tporyzala/tensile-tester/cad/Fixtures/Tensile Gripper Assy 7x7mm.SLDASM

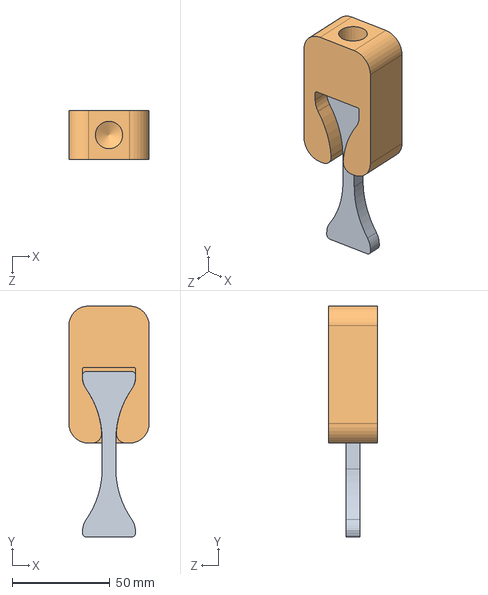
[picture p3: CAD file, 2026-06-16]
cad/Fixtures/Tensile Gripper Assy 7x7mm.SLDASM
41.0 x 117.9 x 25.0 mm
Tensile Gripper 7x7mm
Tensile Coupon 7x7mm
