tporyzala/tensile-tester/cad/Structure/Control Box Face.SLDPRT

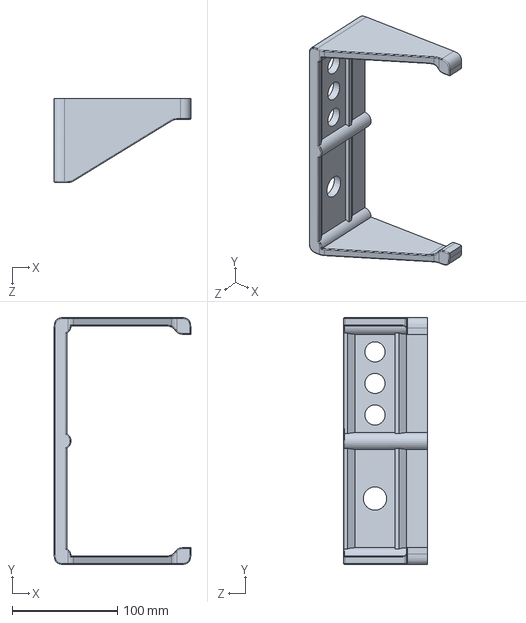
[picture p18: CAD file, 2026-06-02]
cad/Structure/Control Box Face.SLDPRT
130.0 x 235.0 x 80.0 mm
