tporyzala/tensile-tester/cad/toPrint/Tensile Gripper 7x7mm.STEP

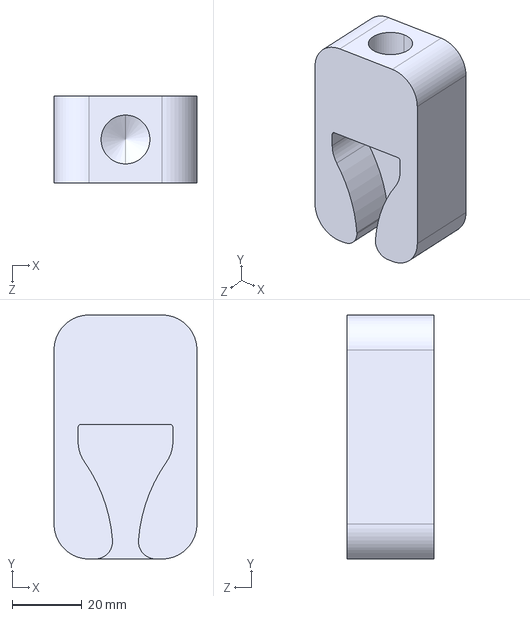
[picture p19: CAD file, 2026-06-16]
cad/toPrint/Tensile Gripper 7x7mm.STEP
41.0 x 70.0 x 25.0 mm
