tporyzala/tensile-tester/cad/Electronics/GX-16 Connector 6 Pins.SLDPRT

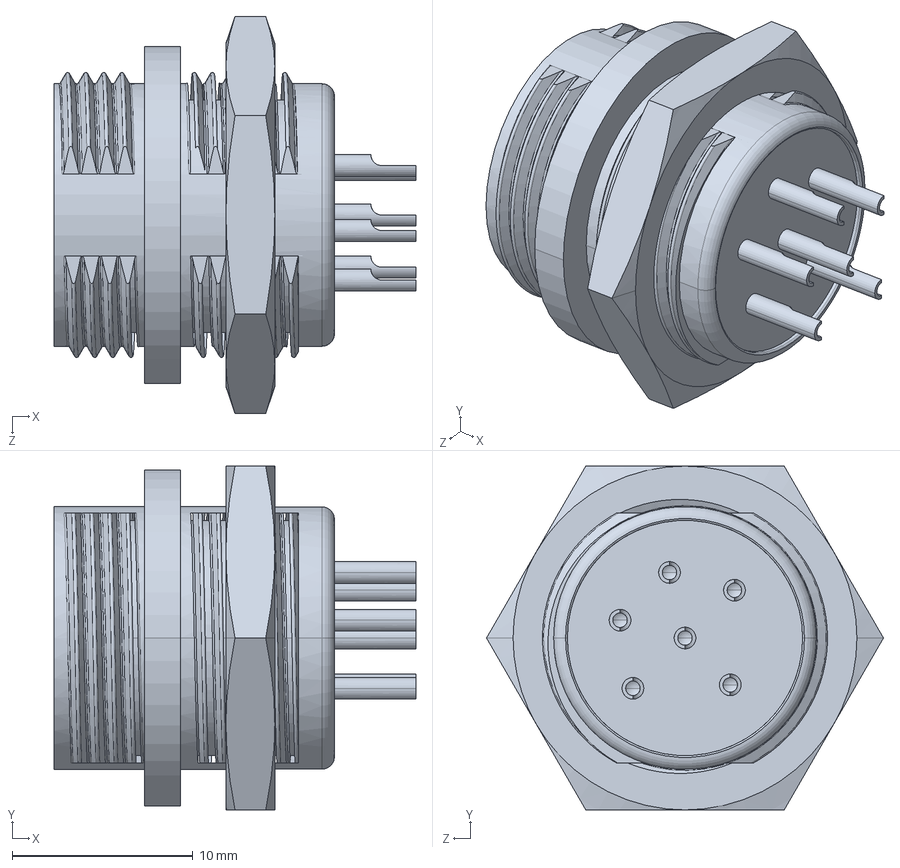
[picture p20: CAD file, 2026-01-30]
cad/Electronics/GX-16 Connector 6 Pins.SLDPRT
20.0 x 19.0 x 21.9 mm
