tporyzala/tensile-tester/cad/MGN9/MGN9 Rail.SLDPRT

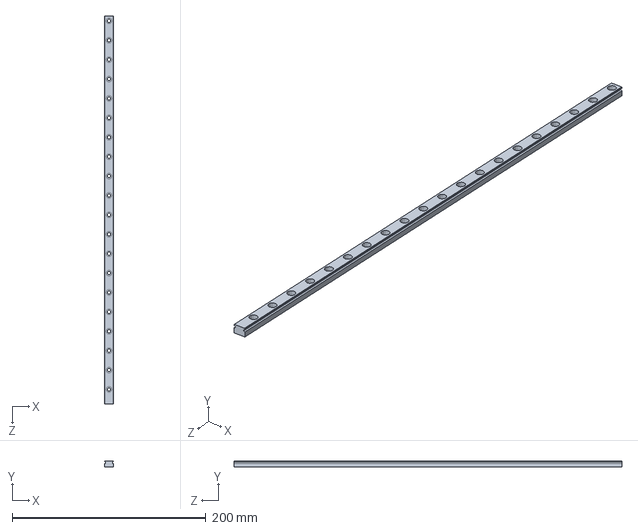
[picture p21: CAD file, 2025-11-23]
cad/MGN9/MGN9 Rail.SLDPRT
9.00 x 6.50 x 400.0 mm
