tporyzala/tensile-tester/cad/SFU/FK10.SLDPRT

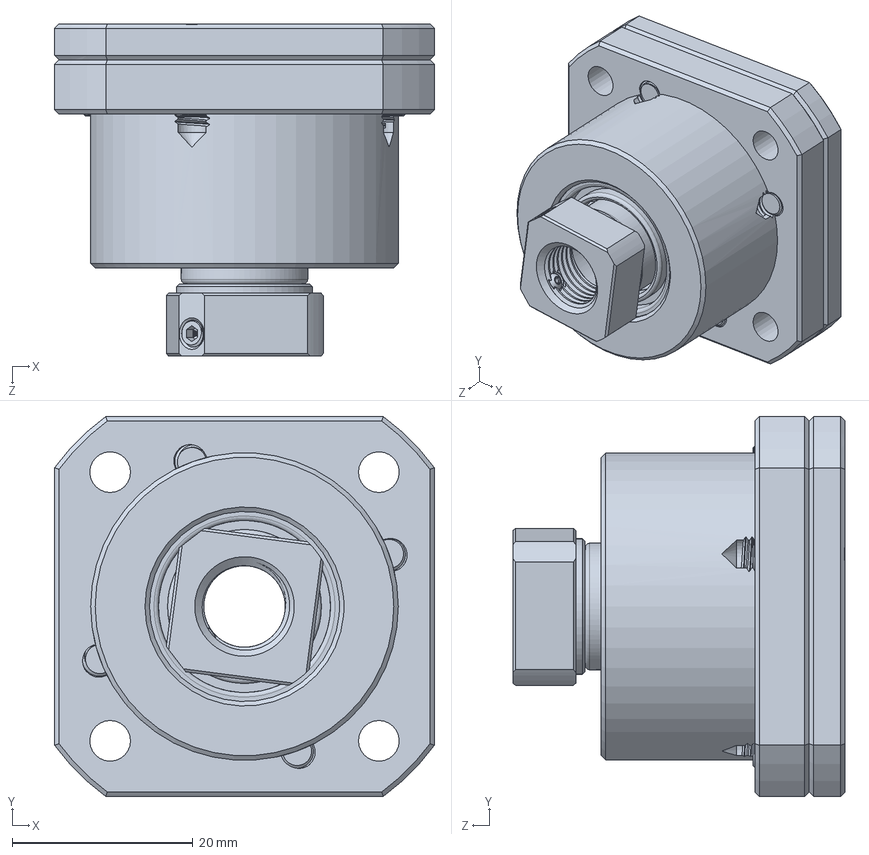
[picture p22: CAD file, 2025-11-23]
cad/SFU/FK10.SLDPRT
42.0 x 42.0 x 36.7 mm
