tporyzala/tensile-tester/cad/Structure/Control Box Base.SLDPRT

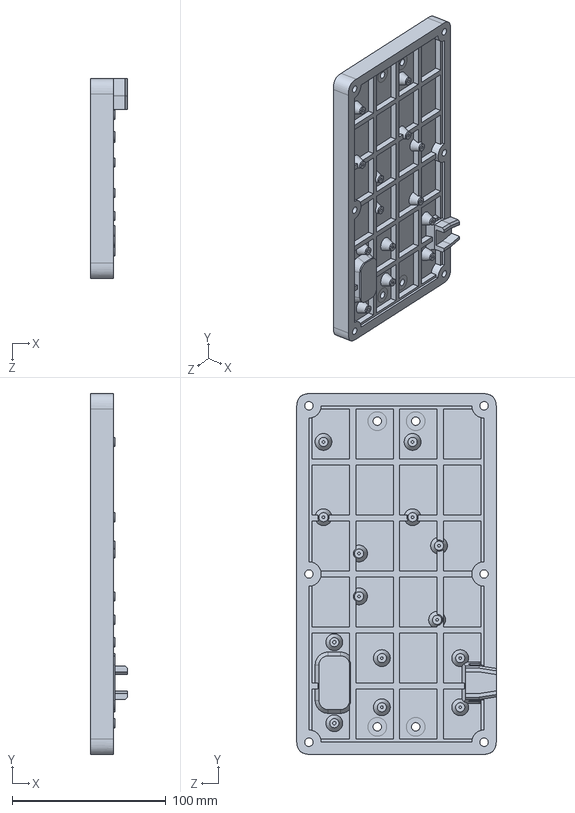
[picture p23: CAD file, 2026-06-02]
cad/Structure/Control Box Base.SLDPRT
24.0 x 235.0 x 130.0 mm
