tporyzala/tensile-tester/cad/toPrint/Tensile Coupon 7x7mm.STEP

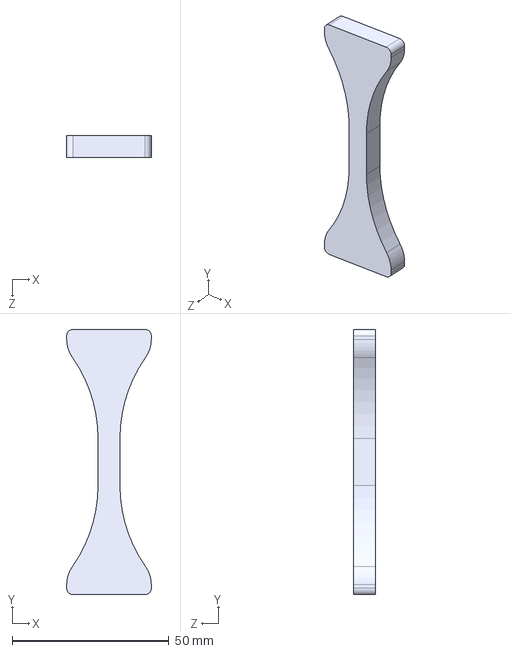
[picture p24: CAD file, 2026-06-16]
cad/toPrint/Tensile Coupon 7x7mm.STEP
27.0 x 84.5 x 7.00 mm
