tporyzala/tensile-tester/cad/Electronics/dc-dc converter.SLDPRT

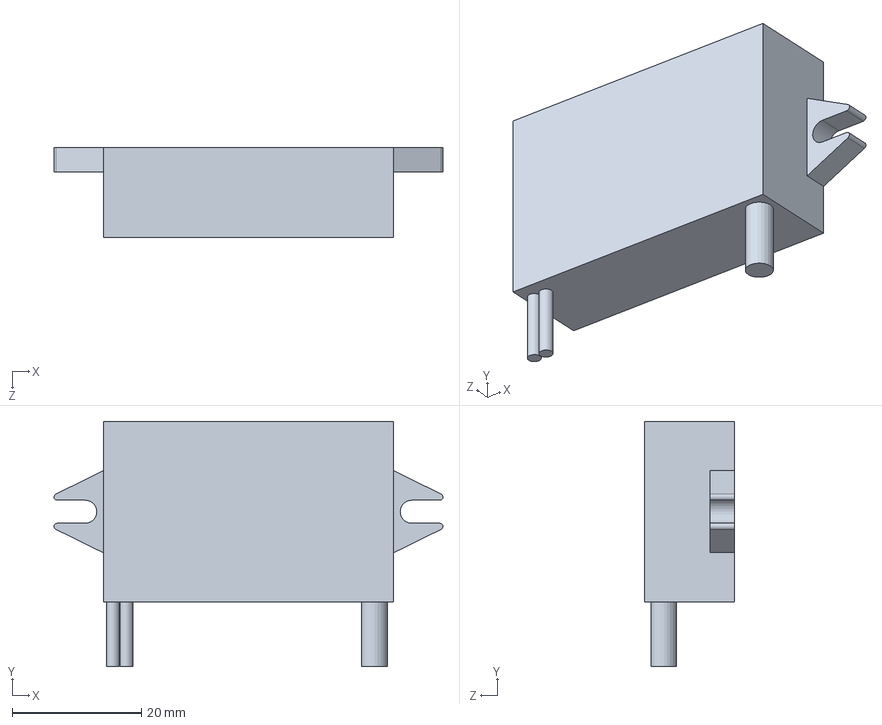
[picture p25: CAD file, 2026-01-26]
cad/Electronics/dc-dc converter.SLDPRT
60.3 x 38.0 x 14.0 mm
