tporyzala/tensile-tester/cad/SFU/BF10.SLDPRT

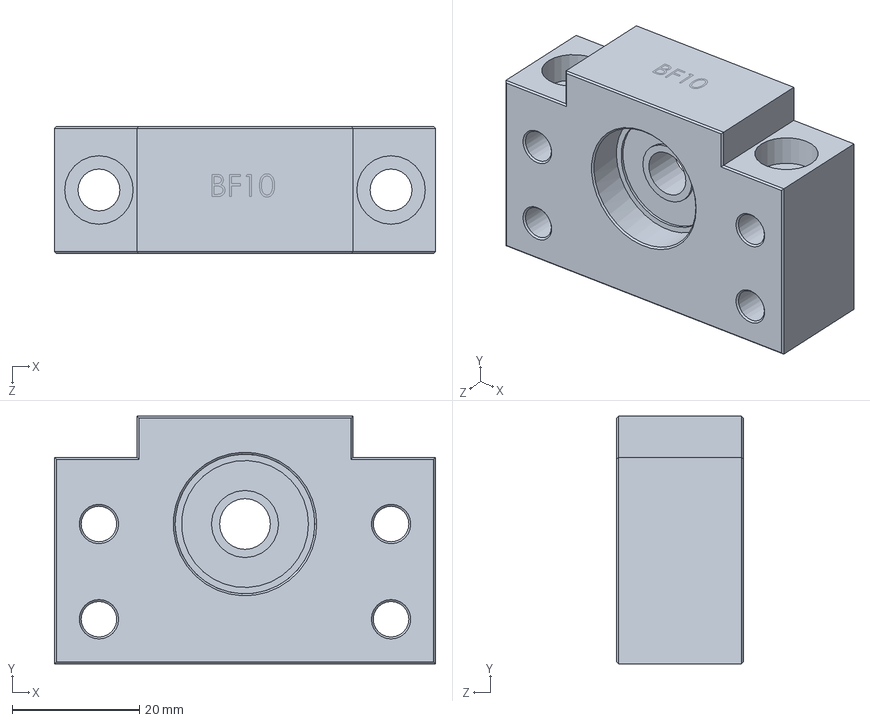
[picture p26: CAD file, 2025-11-23]
cad/SFU/BF10.SLDPRT
60.0 x 39.0 x 20.0 mm
