tporyzala/tensile-tester/cad/Structure/Amplifier Mount Block.SLDPRT

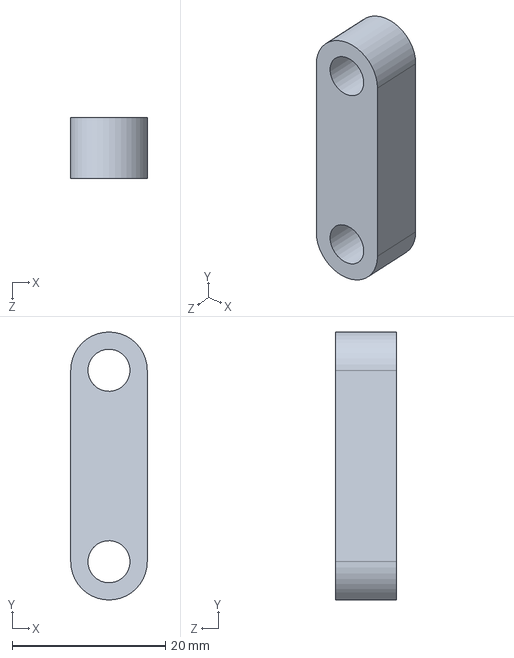
[picture p27: CAD file, 2026-05-17]
cad/Structure/Amplifier Mount Block.SLDPRT
10.0 x 35.0 x 8.00 mm
