tporyzala/tensile-tester/cad/Electronics/power distribution board.SLDPRT

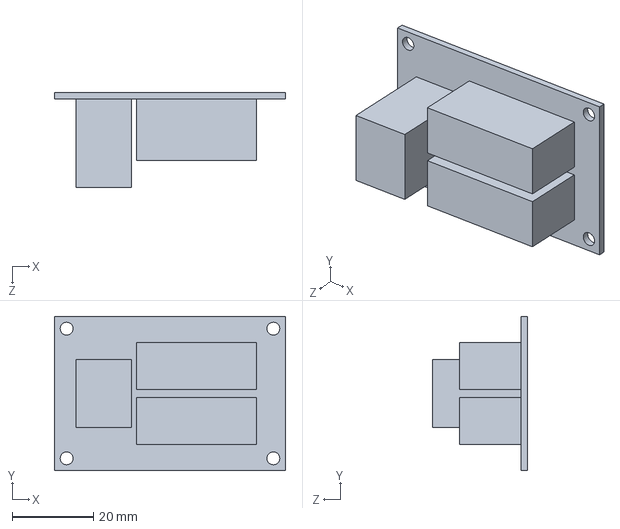
[picture p28: CAD file, 2026-01-26]
cad/Electronics/power distribution board.SLDPRT
57.0 x 38.0 x 23.4 mm
