tporyzala/tensile-tester/cad/SFU/SFU1204 Block.SLDPRT

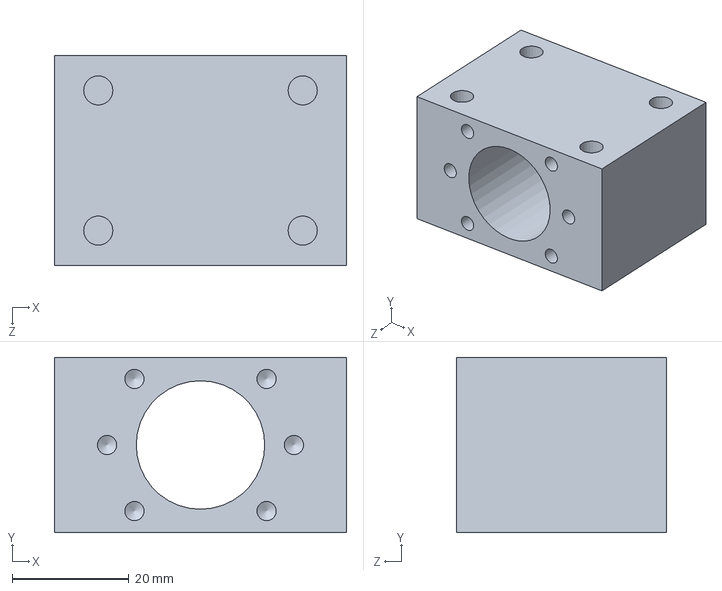
[picture p29: CAD file, 2025-11-23]
cad/SFU/SFU1204 Block.SLDPRT
50.0 x 30.0 x 36.0 mm
