tporyzala/tensile-tester/cad/toPrint/Amplifier Mount.STEP

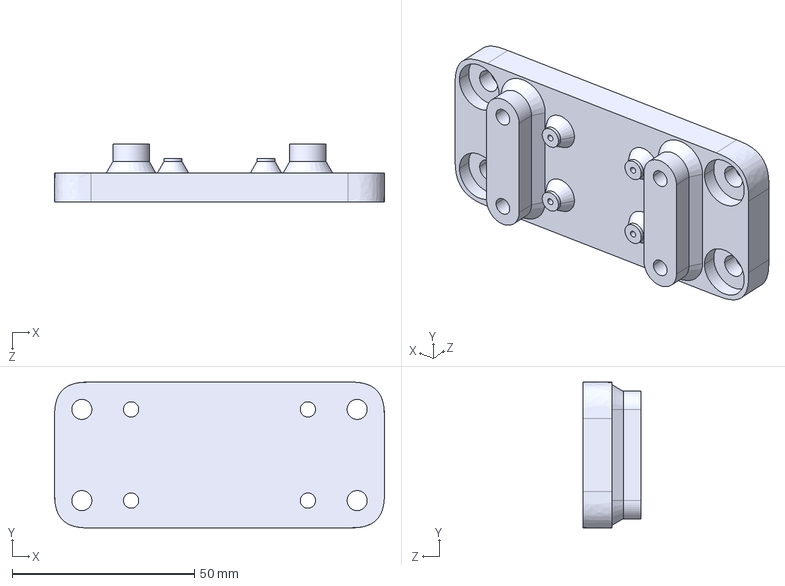
[picture p30: CAD file, 2026-05-17]
cad/toPrint/Amplifier Mount.STEP
90.5 x 40.0 x 16.0 mm
