tporyzala/tensile-tester/cad/Electronics/Raspberry Pi 4 Model B.SLDPRT

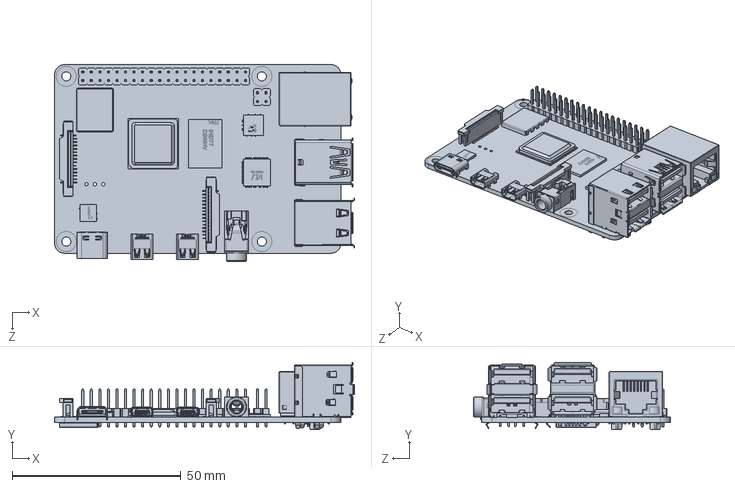
[picture p31: CAD file, 2026-01-25]
cad/Electronics/Raspberry Pi 4 Model B.SLDPRT
89.0 x 19.9 x 58.4 mm
