tporyzala/tensile-tester/cad/Structure/Top Face Plate.SLDPRT

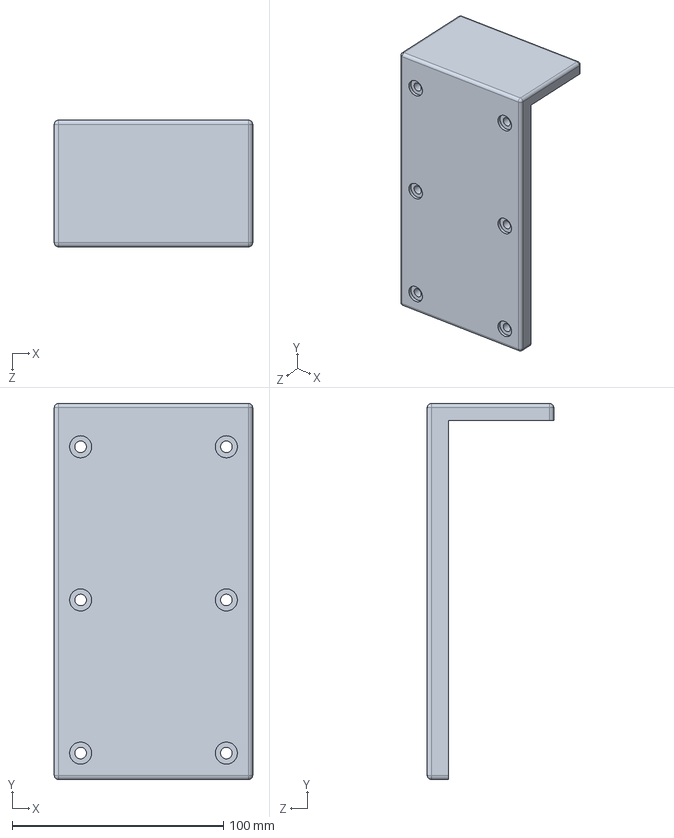
[picture p32: CAD file, 2026-01-17]
cad/Structure/Top Face Plate.SLDPRT
94.0 x 178.0 x 60.0 mm
