tporyzala/tensile-tester/cad/Electronics/HX711.SLDPRT

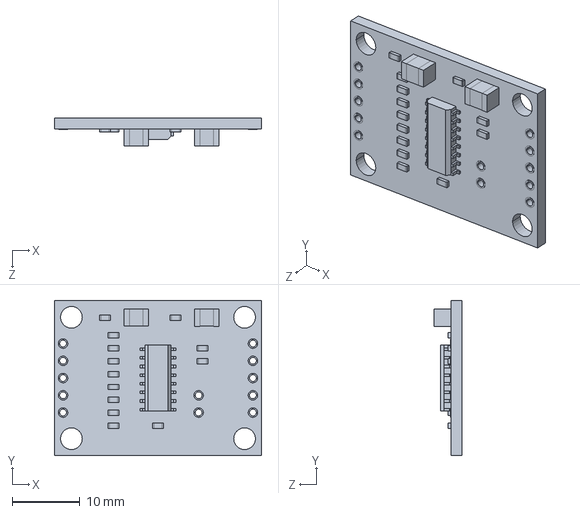
[picture p33: CAD file, 2026-01-25]
cad/Electronics/HX711.SLDPRT
30.5 x 22.9 x 4.10 mm
