tporyzala/tensile-tester/cad/Structure/Top plate column.SLDPRT

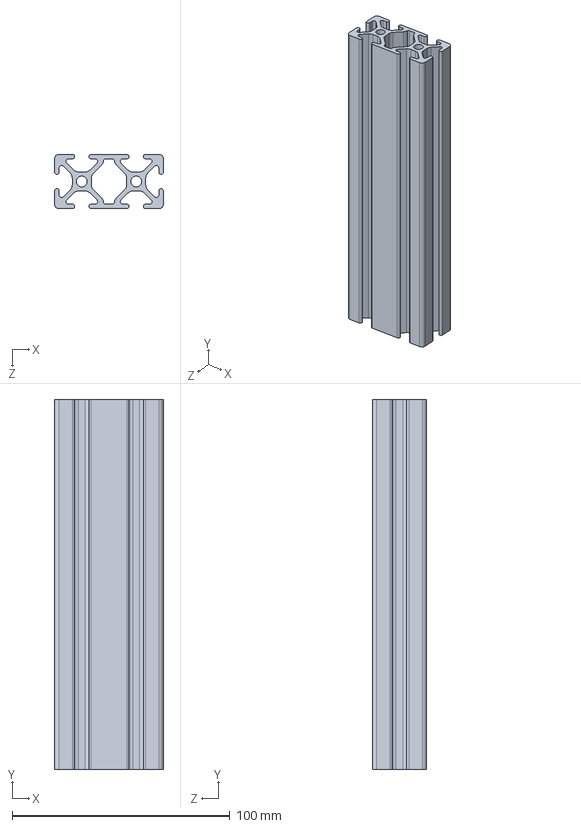
[picture p34: CAD file, 2025-12-22]
cad/Structure/Top plate column.SLDPRT
50.0 x 170.0 x 25.0 mm
