tporyzala/tensile-tester/cad/toPrint/8020 Cable Cap Clip 5mm.STEP

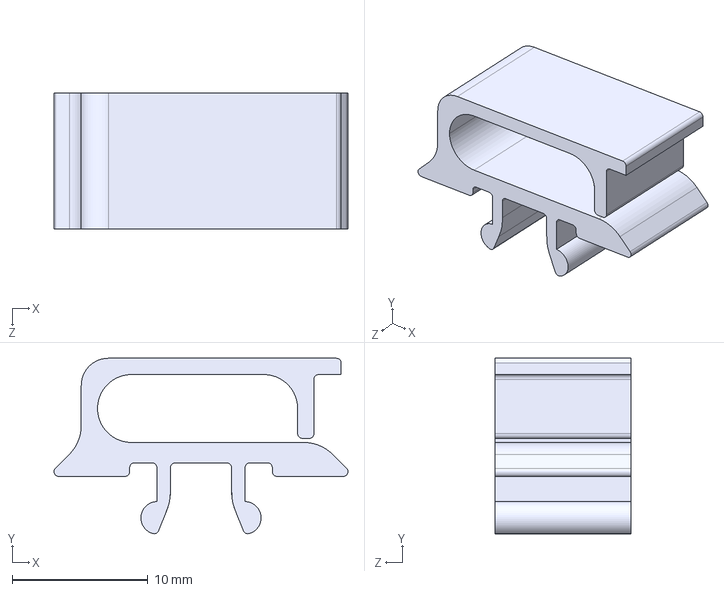
[picture p35: CAD file, 2026-05-13]
cad/toPrint/8020 Cable Cap Clip 5mm.STEP
21.6 x 12.9 x 10.0 mm
