tporyzala/tensile-tester/cad/Electronics/arduino uno.SLDPRT

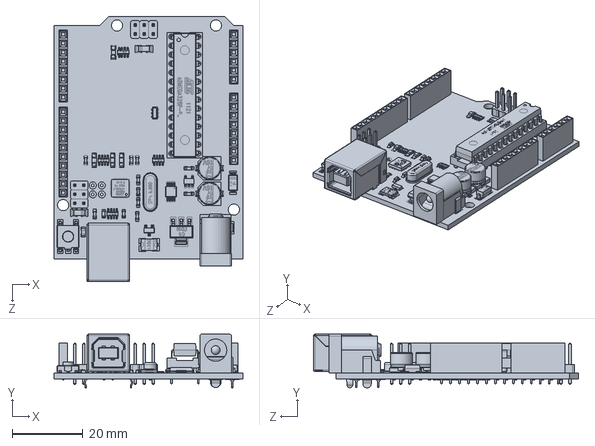
[picture p36: CAD file, 2026-01-25]
cad/Electronics/arduino uno.SLDPRT
53.3 x 15.2 x 74.9 mm
