tporyzala/tensile-tester/cad/Hardware/S load cell.SLDPRT

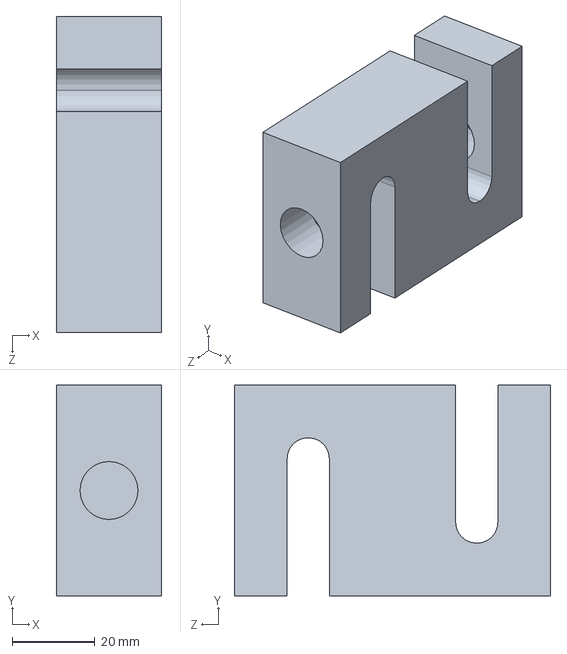
[picture p37: CAD file, 2026-01-12]
cad/Hardware/S load cell.SLDPRT
25.4 x 50.8 x 76.2 mm
