tporyzala/tensile-tester/cad/Structure/Base Plate.SLDPRT

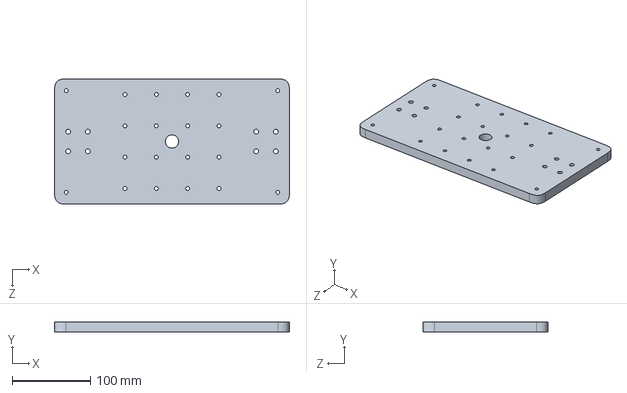
[picture p38: CAD file, 2025-12-22]
cad/Structure/Base Plate.SLDPRT
300.0 x 12.7 x 160.0 mm
