tporyzala/tensile-tester/cad/Electronics/TB6600 - Driver Motor de Passo 4A.stp

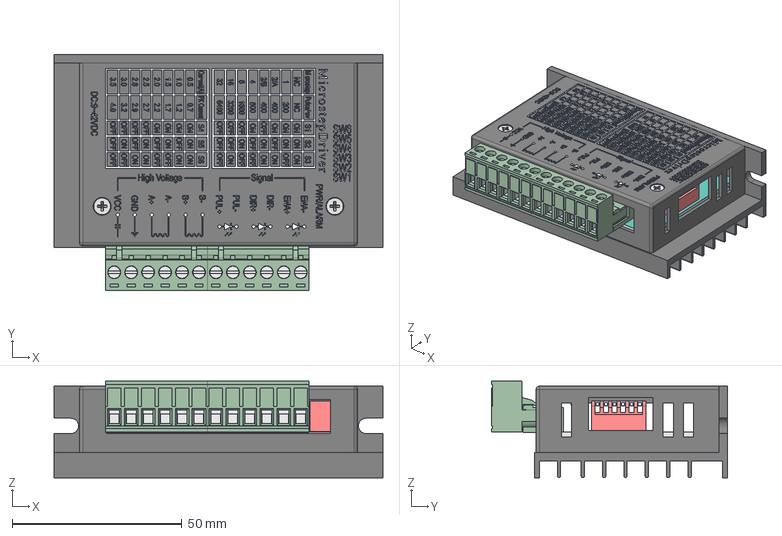
[picture p39: CAD file, 2026-01-12]
cad/Electronics/TB6600 - Driver Motor de Passo 4A.stp
97.0 x 69.6 x 28.5 mm
