tporyzala/tensile-tester/cad/Structure/Top Plate.SLDPRT

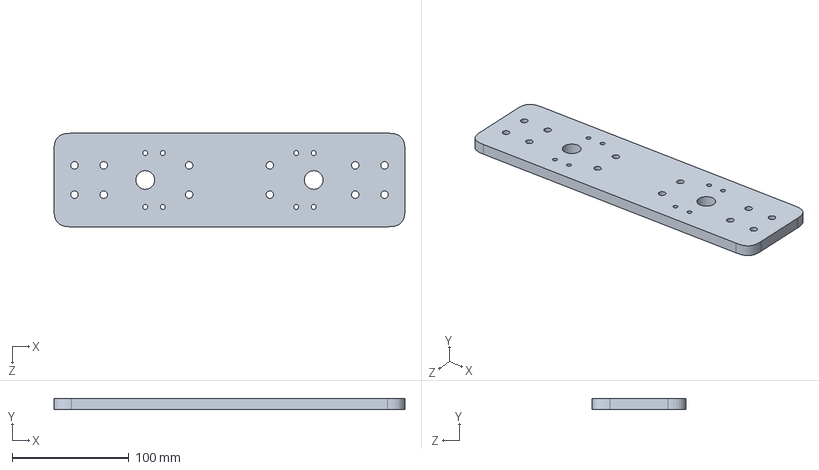
[picture p40: CAD file, 2025-12-22]
cad/Structure/Top Plate.SLDPRT
300.0 x 9.53 x 80.0 mm
