tporyzala/tensile-tester/cad/Structure/Column.SLDPRT

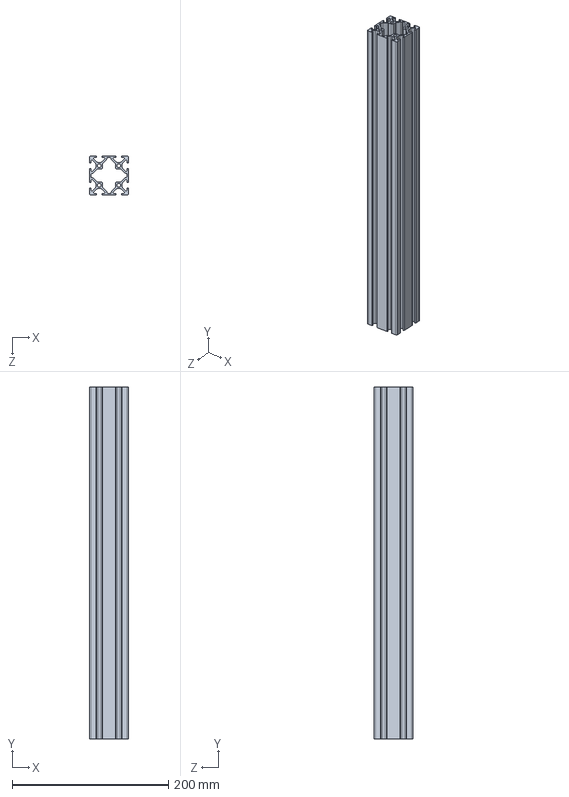
[picture p41: CAD file, 2025-12-22]
cad/Structure/Column.SLDPRT
50.0 x 450.0 x 50.0 mm
