tporyzala/tensile-tester/cad/toPrint/Arduino Platform.STEP

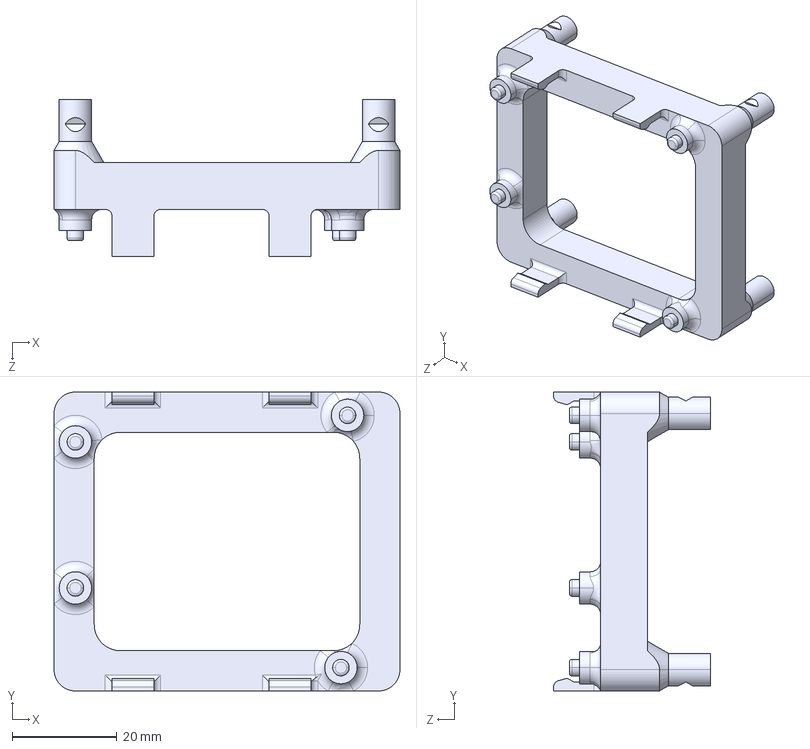
[picture p42: CAD file, 2026-01-29]
cad/toPrint/Arduino Platform.STEP
66.2 x 57.2 x 30.0 mm
