tporyzala/tensile-tester/cad/Structure/Cross Head.SLDPRT

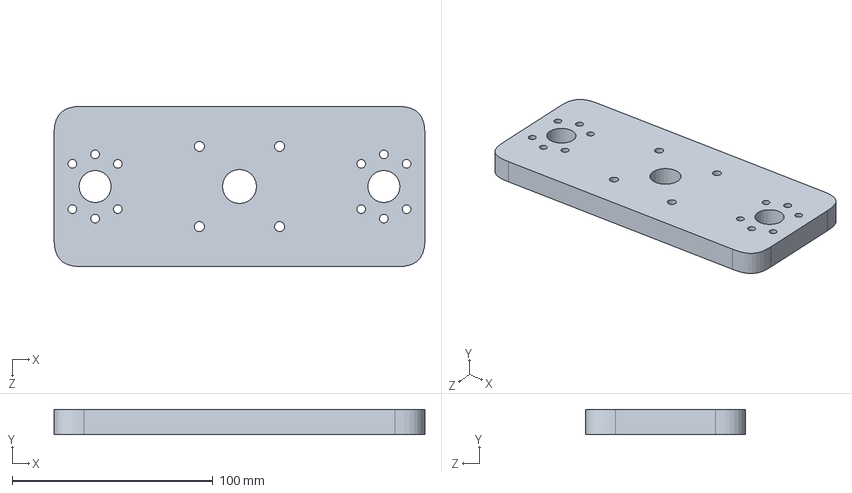
[picture p43: CAD file, 2025-12-22]
cad/Structure/Cross Head.SLDPRT
185.0 x 12.7 x 80.0 mm
