tporyzala/tensile-tester/cad/toPrint/RPI Platform.STEP

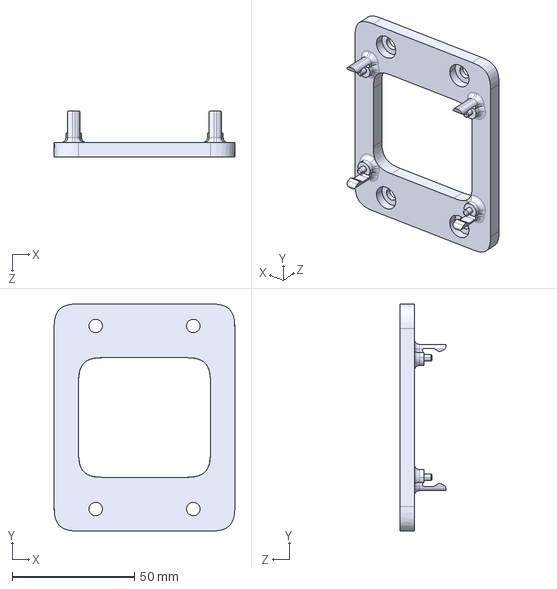
[picture p44: CAD file, 2026-01-29]
cad/toPrint/RPI Platform.STEP
74.0 x 93.0 x 19.0 mm
