tporyzala/tensile-tester/cad/toPrint/v1 print.3mf

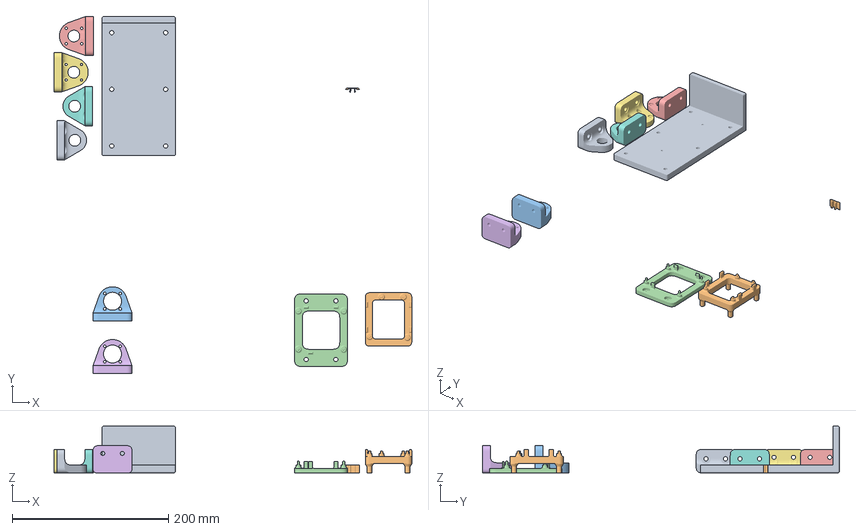
[picture p45: CAD file, 2026-01-28]
cad/toPrint/v1 print.3mf
457.5 x 456.9 x 60.0 mm
Top Face Plate.STEP
Arduino Platform.STEP
Motor bracket.STEP x 4
RPI Platform.STEP
Ballscrew bearing mount.STEP x 2
8020 Cable Cap.STEP
