tporyzala/tensile-tester/cad/Hardware/Coupler 8-8mm.SLDPRT

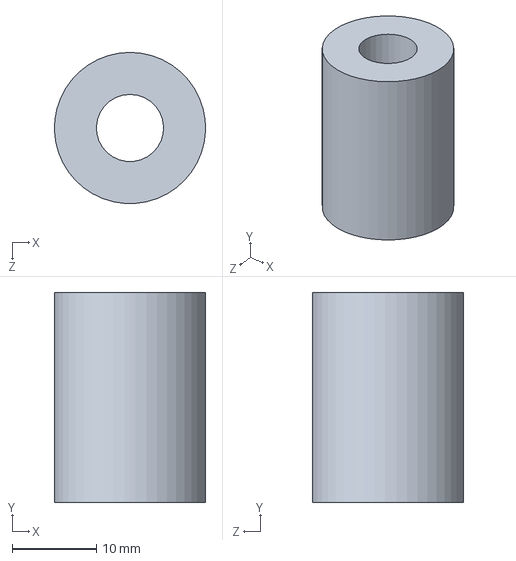
[picture p46: CAD file, 2025-12-23]
cad/Hardware/Coupler 8-8mm.SLDPRT
18.0 x 25.0 x 18.0 mm
