tporyzala/tensile-tester/cad/Hardware/rubber feet.SLDPRT

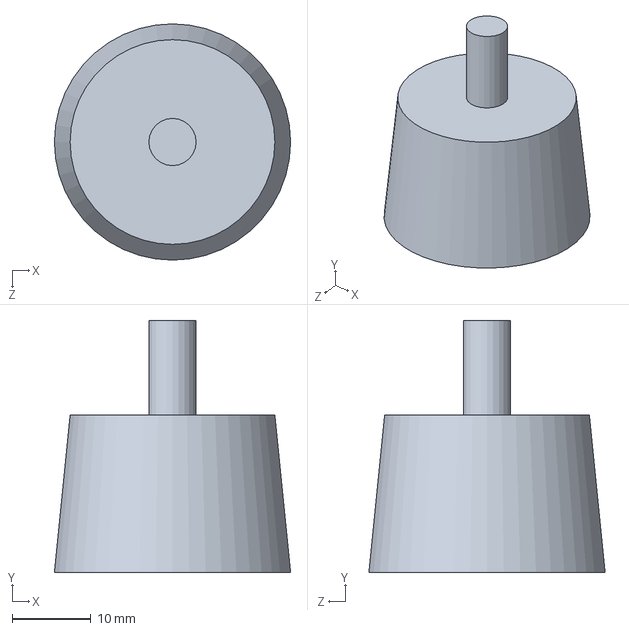
[picture p47: CAD file, 2025-12-17]
cad/Hardware/rubber feet.SLDPRT
30.0 x 32.0 x 30.0 mm
