tporyzala/tensile-tester/cad/Control Box Assy.SLDASM

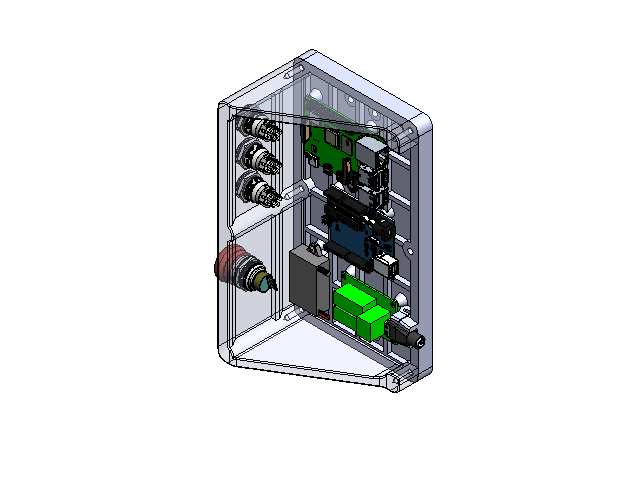
[picture p48: CAD file, 2026-06-02]
cad/Control Box Assy.SLDASM
Control Box Base
arduino uno
Raspberry Pi 4 Model B
dc-dc converter
power distribution board
dc_power_jack_assembly
#2 5-16in 90065A078_18-8 Stainless Steel Phillips Flat Head Screws for Metal x 12
#5 0p5in 92470A121_Phillips Rounded Head Screws for Sheet Metal x 2
Control Box Face
Push Button M19 x 3
22mm E-Stop
