tporyzala/tensile-tester/cad/HX711 Box.SLDASM

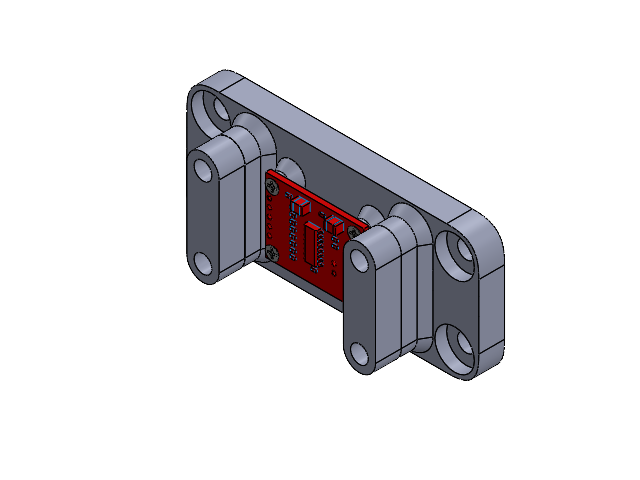
[picture p49: CAD file, 2026-05-17]
cad/HX711 Box.SLDASM
HX711
Amplifier Mount
Amplifier Mount Block x 2
#2 5-16in 90065A078_18-8 Stainless Steel Phillips Flat Head Screws for Metal x 4
